MOSH-Insa-Toulouse/2019_MOSH_PROJECT_JLTT/LTSpice/Adapter_Circuit.asc

C1: cap; 100n
C2: cap; 100n
C3: cap; 100n
C4: cap; 1µ
I1: current; PULSE(-50n -100n 1 0.1 0.1 2); AC 1 0
R1: res; 100k
R2: res; 1k
R3: res; 100k
R4: res; 10k
R5: res; 1k
U1: LTC1050
V1: voltage; 5
Named nets: 0
.ac dec 200 0.01 0.1G
